KarpelesLab/odeck/docs/research/jlcpcb.md

# JLCPCB capabilities (researched 2026-10-02)

[V] = verified on jlcpcb.com, [C] = community/third-party, [I] = inference. Re-verify before ordering.

## Stackup & material
- Impedance control 4L+; ±10% std, ±5% on request [V].
- 4–8L: Nan Ya NP-155F (TG155) — **must order TG155** for the impedance stackups to apply. Df ≈ 0.02 (standard loss) [V].
  **Material options are broader than the impedance-calculator stackups — TO VERIFY in the order form:**
  - JLC blog claims Shengyi, Panasonic Megtron, Rogers, Isola are available [C — marketing, no layer counts]:
    https://jlcpcb.com/blog/low-df-materials-high-speed-pcb
  - Capabilities page: FR-4 from Nan Ya / KB / Shengyi; HDI on NP-175F or S1000-2M (TG170) [V].
  - High-frequency page lists RO4350B + several PTFE (ZYF) laminates, but only for 2L [V]:
    https://jlcpcb.com/pcb-fabrication/high-frequency-pcb
  - User confirmed (2026-10-02) via order-form screenshot: Standard PCB base materials = FR-4, Flex, Aluminum,
    Copper Core, Rogers, PTFE Teflon, HDI. Layers 1/2/4, "High Precision PCB" 6–16+. Separate
    "Advanced PCB/PCBA" product tab (likely where special stackups/materials live — to check).
  - User (2026-10-02): JLC offers up to 32L FR-4, with several FR-4 material choices even within FR-4.
    PCBWay or other fabs acceptable if needed; JLC preferred (user has experience with it).
  - Open question: exact multilayer/hybrid options and pricing for a low/mid-loss build (Megtron 4/6, S1000-2M, hybrid RO4350B outer) orderable at 8L, and at what price?
  - Fallback if only NP-155F: ~1 dB/in @ 10 GHz; keep 20 Gbps/lane runs ≪ 2–3 in or add re-timers/redrivers.
- 8L 1.6 mm: JLC08161H-1080 / -1080A / -1080B / -2116 / -2116A / -7628 [V/C].
  KiCad stackup files: https://github.com/gsuberland/jlcpcb_autogenerated_stackups
- 85–90 Ω diff estimate (JLC08161H-1080) [I]: outer ~0.11 mm w / 0.10–0.13 mm s; inner stripline ~0.16–0.18 mm w / 0.15–0.20 mm s. Confirm in JLC calculator.

## Fab rules
- 0.09/0.09 mm trace/space, 0.15 mm min drill, via 0.15/0.25 mm [V].
- Via-in-pad (POFV, epoxy filled + capped) **free on 6–20 layers**, holes 0.15–0.55 mm [V].
- HDI 1–3 step, laser microvias 0.075–0.15 mm [V]. **Up to 24 layers in HDI mode** (user, 2026-10-02 — the "up to 8L" from the help FAQ is outdated).
- Back-drill 4–32L, holes 0.2–0.5 mm, +1–2 days [V].

## Assembly
- **Standard PCBA required** (Economic stops at 0.5 mm BGA / 0402) — BGA to 0.35 mm pitch, X-ray automatic [V].
- Double-sided supported (setup $51.12, stencil $16.42); extended parts $3/unique part [V].
- Standard PCBA min board 70×70 mm → 100×60 needs edge rails/panel [V/I].
- **Sourcing strategy (decided 2026-10-02):** parts not in LCSC stock are bought from Mouser/DigiKey and shipped to JLC as consigned parts.
- Consigned parts allowed (restrictions on mixing with stock) [V/C]; Global Sourcing for non-LCSC parts.
- **Programming: post-solder only, via an on-board interface, engineering-review, ~$7.86 + $7.86/h; no pre-programming of SPI flash** [V/C].
  → "works on arrival" must rely on ROM-boot chips or MCU self-flashing vendor SPI flash on first boot.

## Aesthetics
- Mask: green/purple/red/yellow/blue/white/black on all layer counts; matte black discontinued [V/C].
- **Full-color silkscreen only for 2–4L white boards, EasyEDA Pro only → not usable for us** [V].
  → Single-color silk + ENIG exposed-copper art; 6L+ ships ENIG.
- Silk min 0.15 mm line / 1.0 mm text height [V]. Castellations, edge plating available.

## High-speed precedent
- No JLC-specific USB4 guidance or confirmed compliant JLC-built USB4/TB board found.
- Closest public: cartouche-usb4 (ASM2464PD, 4L, 0.46 mm BGA, unvalidated) — https://github.com/opencorp2030-ctrl/cartouche-usb4
- Plan: 8L TG155, ±5% impedance, pairs on L1 over thin 1080 prepreg, short; POFV under BGAs; back-drill layer-changing 20G pairs; redriver/retimer budget.
