KarpelesLab/odeck/hardware/odeck-10/layout/power.py

"""odeck-10 placement: power block (sheets "Power input" + "Laptop power out", plus U1201/C1201/TH1201/TP1201).

Region (100,50)-(138,108). Generated from a hand-placed skeleton (connectors, TVS, power stages, source switch)
plus an anchor-driven packer for the small parts (each part next to the pin/part it serves), then frozen here as
explicit coordinates. Rationale and routing intent: docs/layout-notes/power.md.
Coordinates are footprint origins in mm (absolute), rotation in degrees, side 'top' | 'bottom'.
"""

REGION = [(100.0, 50.0, 138.0, 108.0),
          (100.0, 49.5, 138.0, 64.0)]   # J101/J102 courtyards overhang the back edge by 0.5 mm (mating face flush)

REFS = [
    'C101', 'C102', 'C103', 'C104', 'C105', 'C106', 'C107', 'C108', 'C109', 'C110', 'C111', 'C112', 'C113', 'C114',
    'C115', 'C116', 'C117', 'C118', 'C119', 'C120', 'C121', 'C122', 'C123', 'C124', 'C125', 'C201', 'C202', 'C203',
    'C204', 'C205', 'C206', 'C207', 'C208', 'C209', 'C210', 'C211', 'C212', 'C213', 'C214', 'C215', 'C216', 'C217',
    'C218', 'C219', 'C220', 'C221', 'C222', 'C223', 'C224', 'C225', 'C226', 'C227', 'C228', 'C229', 'C230', 'C231',
    'C232', 'C233', 'C234', 'C235', 'C236', 'C237', 'C238', 'C239', 'C240', 'C241', 'C242', 'C243', 'C244', 'C1201',
    'D101', 'D102', 'D103', 'D201', 'D202', 'D203', 'D204', 'D205', 'D206', 'J101', 'J102', 'L201', 'Q101', 'Q102',
    'Q103', 'Q104', 'Q105', 'Q106', 'Q107', 'Q201', 'Q202', 'Q203', 'Q204', 'Q205', 'Q206', 'Q207', 'Q208', 'Q209',
    'Q210', 'Q211', 'Q212', 'Q213', 'Q214', 'Q215', 'Q216', 'Q217', 'Q218', 'Q219', 'Q220', 'Q221', 'R101', 'R102',
    'R103', 'R104', 'R105', 'R106', 'R107', 'R108', 'R109', 'R110', 'R111', 'R112', 'R113', 'R114', 'R115', 'R116',
    'R117', 'R118', 'R119', 'R120', 'R121', 'R122', 'R123', 'R124', 'R125', 'R126', 'R127', 'R128', 'R129', 'R130',
    'R131', 'R132', 'R133', 'R134', 'R135', 'R136', 'R137', 'R201', 'R202', 'R203', 'R204', 'R205', 'R206', 'R207',
    'R208', 'R209', 'R210', 'R211', 'R212', 'R213', 'R214', 'R215', 'R216', 'R217', 'R218', 'R219', 'R220', 'R221',
    'R222', 'R223', 'R224', 'R225', 'R226', 'R227', 'R228', 'R229', 'R230', 'R231', 'R232', 'R233', 'R234', 'R235',
    'R236', 'R237', 'R238', 'R239', 'R240', 'R241', 'R242', 'R243', 'R244', 'R245', 'R246', 'R247', 'R248', 'R249',
    'R250', 'R251', 'R252', 'R253', 'R254', 'R255', 'R256', 'R257', 'R258', 'TH1201', 'TP101', 'TP102', 'TP1201',
    'U101', 'U102', 'U103', 'U104', 'U105', 'U106', 'U107', 'U108', 'U109', 'U201', 'U202', 'U203', 'U204', 'U205',
    'U206', 'U207', 'U1201',
]

PLACEMENT = [
    # --- Edge connectors (mating faces at the back edge; J102 moved right of 108 to clear H1 by 4 mm)
    ('J102', 113.70, 54.35, 180, 'top'),
    ('J101', 126.10, 57.05, 180, 'top'),
    # --- Input TVS diodes on top, at the connectors
    ('D102', 103.85, 64.65, 270, 'top'),
    ('D101', 125.90, 64.15, 180, 'top'),
    ('C101', 132.60, 64.90, 90, 'bottom'),
    ('C102', 128.85, 62.15, 0, 'bottom'),
    ('C115', 103.85, 60.70, 0, 'bottom'),
    # --- Input ideal diodes on the BOTTOM: one row Q106|Q107 || Q105|Q104, common-drain pairs, VIN_OR node between Q107 and Q105
    ('Q106', 104.65, 66.30, 90, 'bottom'),
    ('Q107', 112.10, 66.30, 270, 'bottom'),
    ('Q105', 119.50, 66.30, 90, 'bottom'),
    ('Q104', 126.95, 66.30, 270, 'bottom'),
    ('U105', 108.40, 71.30, 0, 'bottom'),
    ('U104', 117.95, 71.55, 90, 'bottom'),
    ('C116', 109.10, 68.80, 0, 'top'),
    ('C117', 109.80, 74.30, 0, 'bottom'),
    ('C118', 105.40, 71.30, 90, 'bottom'),
    ('R124', 110.55, 75.30, 0, 'top'),
    ('R125', 103.25, 71.30, 90, 'bottom'),
    ('R126', 103.25, 71.80, 0, 'top'),
    ('R127', 102.00, 74.95, 90, 'bottom'),
    ('R128', 101.50, 70.55, 90, 'bottom'),
    ('C112', 123.20, 62.05, 0, 'bottom'),
    ('C113', 120.95, 75.15, 90, 'bottom'),
    ('C114', 110.00, 81.50, 0, 'bottom'),   # moved off R137.2 (VIN vias) 2026-10-03: bottom under the Q203 SW2 EP
    ('R121', 113.95, 78.70, 0, 'bottom'),
    ('R122', 110.30, 80.00, 180, 'bottom'),  # idem (PD_OV pad 1 east, toward R121.2)
    ('R123', 113.70, 64.40, 90, 'top'),
    # --- OR node: 2 mOhm shunt + INA237 (bottom), VIN local decoupling
    ('R137', 113.75, 73.50, 270, 'bottom'),
    ('U109', 117.75, 77.00, 0, 'bottom'),
    ('C125', 120.60, 76.25, 90, 'top'),
    ('C123', 110.75, 72.80, 90, 'top'),
    ('C124', 117.50, 69.80, 0, 'top'),
    ('C122', 132.55, 94.60, 270, 'top'),
    # --- LM51770 4-switch stage, vertical column x 100.6-112.3: boost leg on top (y 71-82), L201, sense R, buck leg (y 93-108)
    ('C205', 106.95, 72.85, 0, 'top'),
    ('C206', 106.95, 76.30, 0, 'top'),
    ('C207', 105.70, 75.90, 0, 'bottom'),
    ('C208', 102.70, 75.40, 90, 'top'),
    ('Q204', 105.95, 80.25, 90, 'top'),
    ('Q203', 110.00, 80.25, 270, 'top'),
    ('L201', 106.30, 87.60, 90, 'top'),
    ('R201', 104.50, 94.75, 0, 'top'),
    ('Q202', 103.50, 100.55, 0, 'top'),
    ('Q201', 109.45, 100.55, 180, 'top'),
    ('C201', 106.50, 106.00, 180, 'top'),
    ('C202', 108.70, 106.25, 0, 'bottom'),
    ('C203', 111.45, 106.25, 0, 'top'),
    ('C204', 103.70, 106.25, 180, 'bottom'),
    ('C214', 113.70, 103.05, 90, 'bottom'),
    ('R202', 115.95, 73.15, 0, 'top'),
    ('C209', 117.45, 76.95, 0, 'top'),
    ('C210', 117.45, 80.40, 0, 'top'),
    ('C211', 126.95, 77.20, 0, 'top'),
    ('C212', 126.95, 84.55, 0, 'top'),
    ('C213', 115.15, 83.10, 0, 'bottom'),
    # --- LM51770 controller (power pins face the column) + drive / sense / analog parts
    ('U201', 118.05, 87.70, 90, 'top'),
    ('R203', 112.85, 93.95, 90, 'top'),
    ('R204', 110.30, 96.05, 0, 'top'),
    ('R205', 112.85, 83.20, 90, 'top'),
    ('R206', 112.80, 85.50, 90, 'top'),
    ('C219', 115.15, 93.95, 0, 'top'),
    ('C220', 115.50, 85.45, 90, 'bottom'),  # HB2 bootstrap under pins 25/26 (pad 1 HB2 under pin 26), 2026-10-03
    ('C221', 115.15, 91.70, 0, 'bottom'),
    ('R210', 108.35, 93.10, 0, 'bottom'),
    ('R211', 111.30, 93.45, 0, 'bottom'),
    ('C215', 123.45, 91.20, 90, 'top'),
    ('C216', 120.95, 92.20, 0, 'bottom'),
    ('C217', 114.90, 88.80, 90, 'bottom'),
    ('C218', 121.20, 87.20, 90, 'bottom'),
    ('R209', 120.95, 93.95, 0, 'top'),
    ('C222', 122.95, 87.70, 90, 'bottom'),
    ('C223', 125.20, 87.70, 0, 'bottom'),
    ('C224', 118.60, 84.60, 0, 'bottom'),   # BB_COMP: under the package above the EP, toward pin 18
    ('C225', 122.95, 89.95, 90, 'bottom'),
    ('C226', 113.95, 81.20, 0, 'bottom'),
    ('C227', 103.05, 106.95, 90, 'top'),
    ('R207', 120.95, 94.20, 0, 'bottom'),
    ('R208', 120.95, 95.45, 0, 'top'),
    ('R212', 124.70, 89.20, 0, 'bottom'),
    ('R213', 124.70, 90.45, 0, 'bottom'),
    ('R214', 123.70, 91.70, 0, 'bottom'),
    ('R215', 121.20, 89.70, 0, 'bottom'),
    ('R216', 118.70, 91.70, 90, 'bottom'),
    ('R217', 118.20, 93.70, 0, 'top'),
    ('R218', 123.70, 93.70, 0, 'top'),
    ('R219', 117.45, 91.70, 90, 'bottom'),
    ('R220', 120.95, 81.20, 90, 'top'),
    ('R221', 120.95, 78.95, 90, 'top'),
    ('R222', 116.70, 81.70, 0, 'bottom'),
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
    ('R136', 132.95, 87.35, 0, 'top'),
    ('C120', 127.30, 89.75, 90, 'bottom'),
    ('U108', 111.75, 86.50, 90, 'bottom'),
    ('C121', 114.20, 85.35, 90, 'bottom'),
]


def place(board, h):
    for ref, x, y, rot, side in PLACEMENT:
        h.put(ref, x, y, rot, side)
